1Jamie/GaiasGamepad/controller_wiring/controller_wiring.kicad_pcb

## KiCad design kicad/10-Clock/10-Clock.kicad_sch

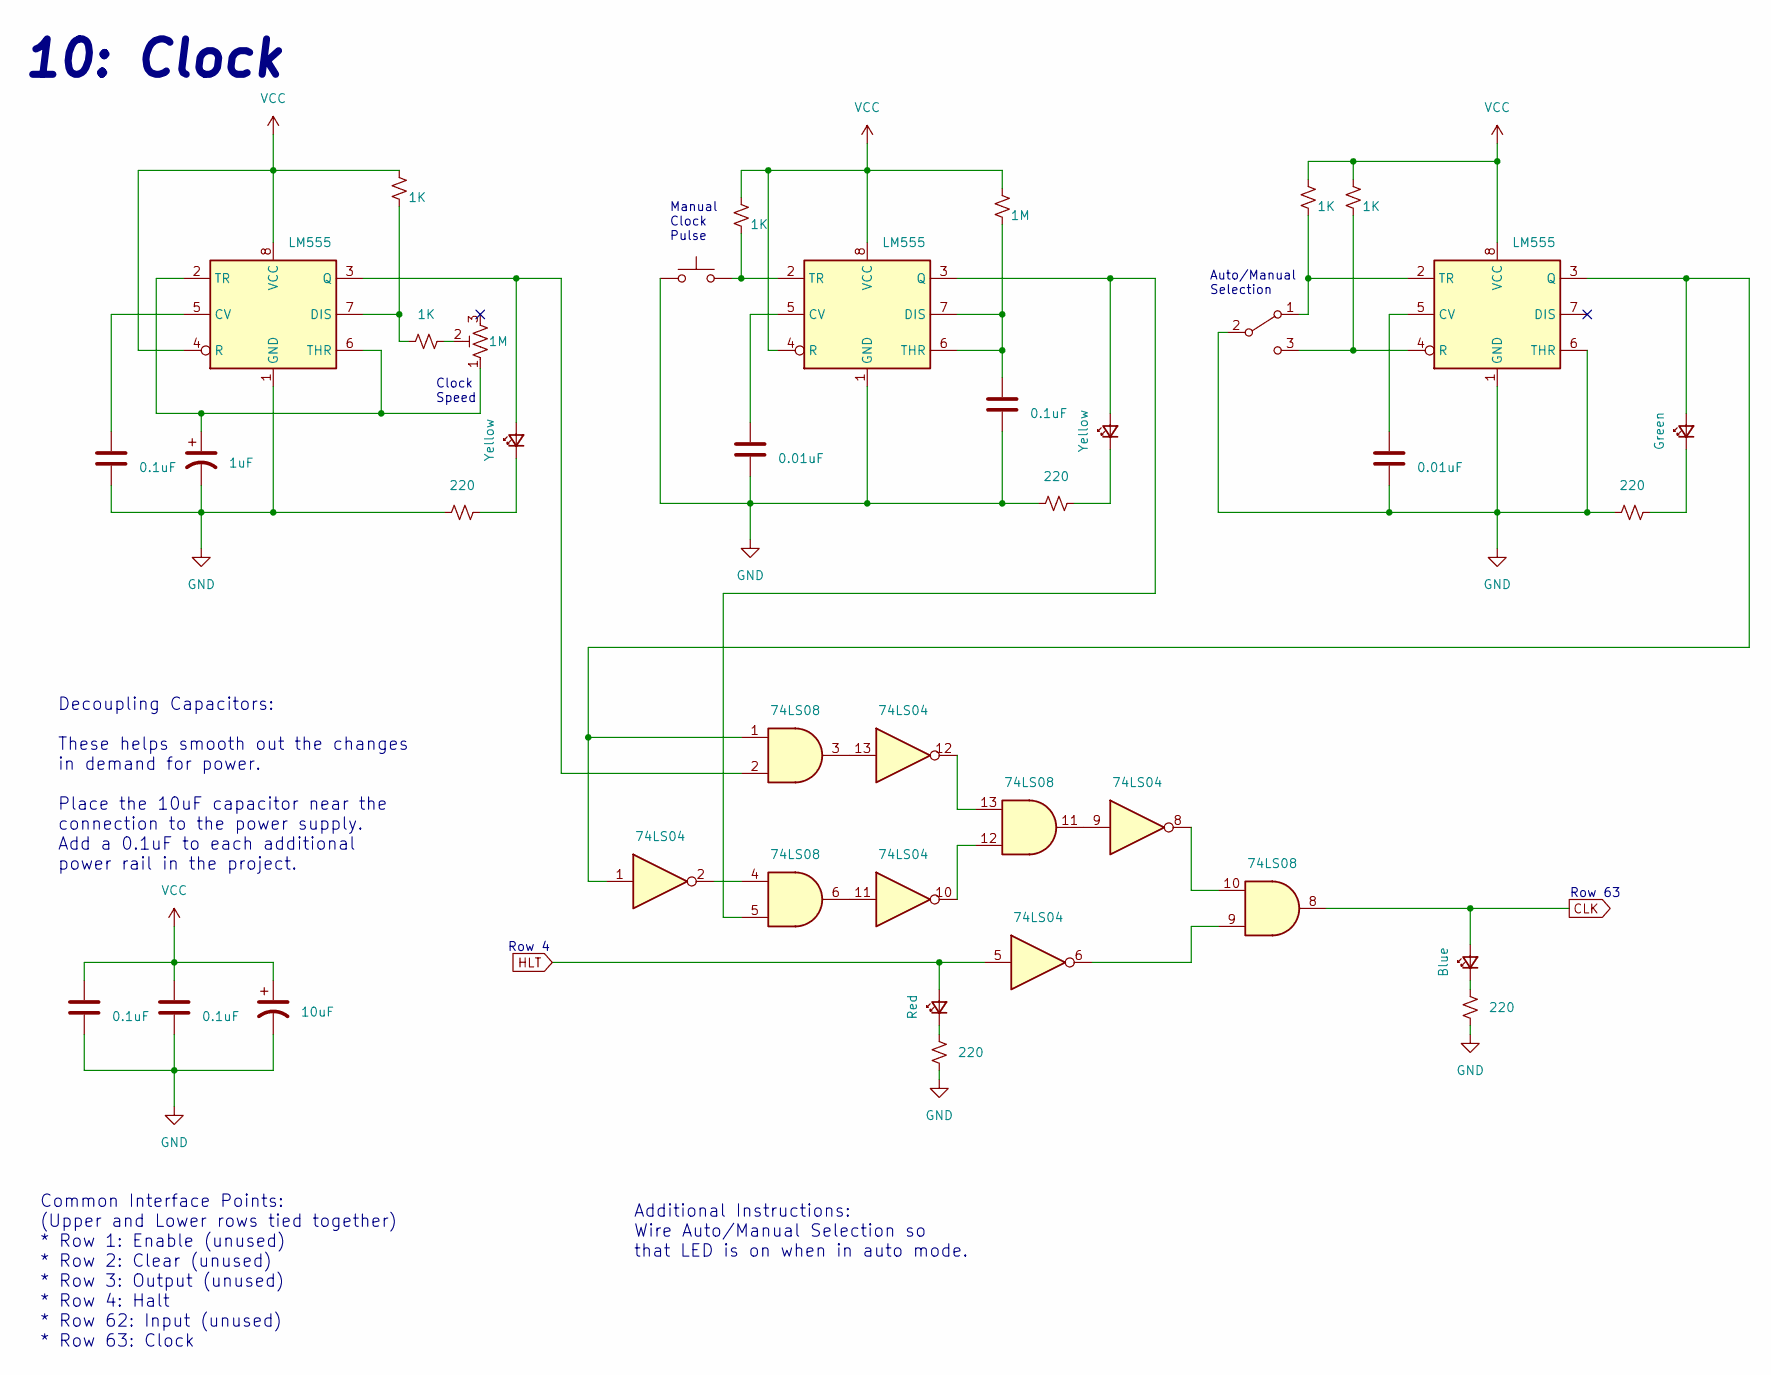
[picture p8: schematic 10-Clock.kicad_sch]

Parts:
C1, C4, C6, C7: 0.1uF
C2: 1uF
C3, C5: 0.01uF
C8: 10uF
D1, D3: Yellow
D2: Red
D4: Blue
D5: Green
R1, R2, R4, R8, R9: 1K
R3, R5, R7, R10, R11: 220
R6: 1M
RV1: 1M
SW1: SW_Push
SW2: SW_SPDT
U1, U4, U5: LM555; SOIC-8_3.9x4.9mm_P1.27mm
U2: 74LS04
U3: 74LS08

Connections:
CLK: D4.2 (A), U3.8
GND: C1.2, C2.2, C3.2, C4.2, C5.2, C6.2, C7.2, C8.2, R3.1, R5.1, R7.1, R10.1, R11.1, SW1.1, SW2.2 (B), U1.1 (GND), U4.1 (GND), U5.1 (GND), U5.6 (THR)
HLT: D2.2 (A), U2.5
unnamed: C1.1, U1.5 (CV)
unnamed: C2.1, RV1.1, U1.2 (TR), U1.6 (THR)
unnamed: C3.1, U4.5 (CV)
unnamed: C4.1, R6.2, U4.6 (THR), U4.7 (DIS)
unnamed: C5.1, U5.5 (CV)
unnamed: D1.1 (K), R3.2
unnamed: D1.2 (A), U1.3 (Q), U3.2
unnamed: D2.1 (K), R5.2
unnamed: D3.1 (K), R7.2
unnamed: D3.2 (A), U3.5, U4.3 (Q)
unnamed: D4.1 (K), R10.2
unnamed: D5.1 (K), R11.2
unnamed: D5.2 (A), U2.1, U3.1, U5.3 (Q)
unnamed: R1.2, R2.1, U1.7 (DIS)
unnamed: R2.2, RV1.2
unnamed: R4.2, SW1.2, U4.2 (TR)
unnamed: R8.2, SW2.1 (A), U5.2 (TR)
unnamed: R9.2, SW2.3 (C), U5.4 (R)
unnamed: U2.2, U3.4
unnamed: U2.6, U3.9
unnamed: U2.8, U3.10
unnamed: U2.9, U3.11
unnamed: U2.10, U3.12
unnamed: U2.11, U3.6
unnamed: U2.12, U3.13
unnamed: U2.13, U3.3
VCC: C6.1, C7.1, C8.1, R1.1, R4.1, R6.1, R8.1, R9.1, U1.4 (R), U1.8 (VCC), U4.4 (R), U4.8 (VCC), U5.8 (VCC)

Notes on the sheet:
Row 63
Manual Clock Pulse
Clock Speed
Common Interface Points: (Upper and Lower rows tied together) * Row 1: Enable (unused) * Row 2: Clear (unused) * Row 3: Output (unused) * Row 4: Halt * Row 62: Input (unused) * Row 63: Clock
Decoupling Capacitors: These helps smooth out the changes in demand for power. Place the 10uF capacitor near the connection to the power supply. Add a 0.1uF to each additional power rail in the project.
Additional Instructions: Wire Auto/Manual Selection so that LED is on when in auto mode.
Auto/Manual Selection
Row 4
10: Clock
